CaioCCosta/indutor-dynavap/caixa-3d/decals/src/tribal_1.jpg

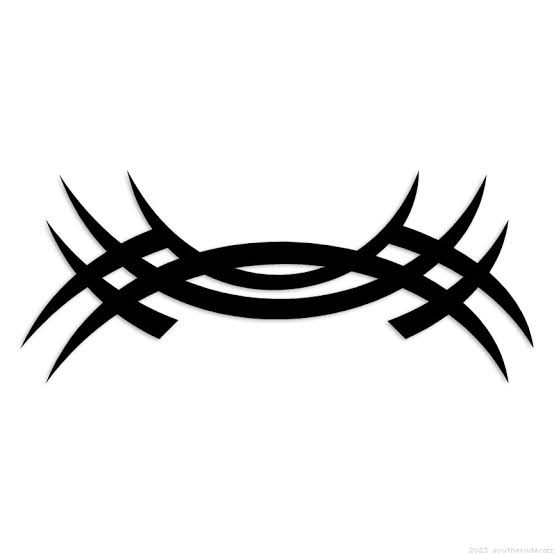
caixa-3d/decals/src/tribal_1.jpg
