CaioCCosta/indutor-dynavap/caixa-3d/decals/src/tribal_2.jpg

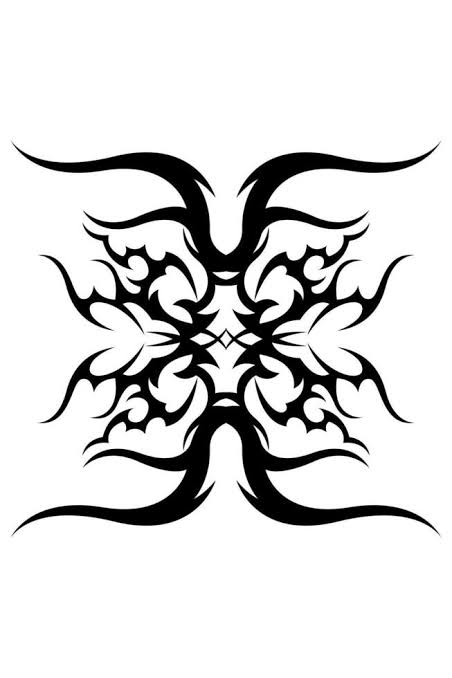
caixa-3d/decals/src/tribal_2.jpg
