CaioCCosta/indutor-dynavap/caixa-3d/stl/previews/body_bottom.png

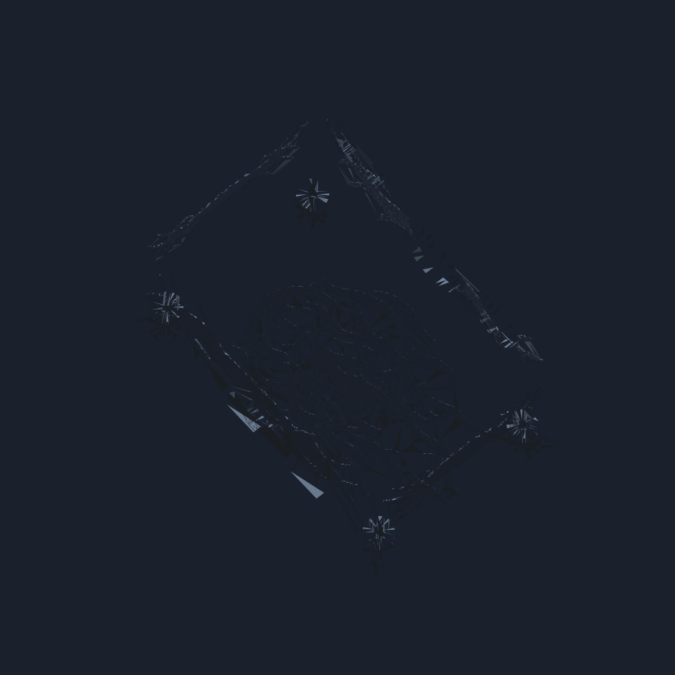
caixa-3d/stl/previews/body_bottom.png
