CaioCCosta/indutor-dynavap/caixa-3d/stl/previews/body_front.png

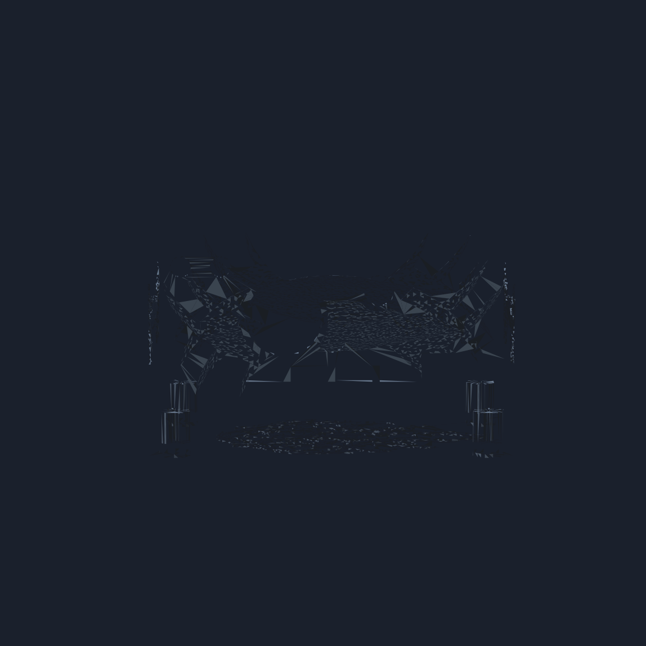
caixa-3d/stl/previews/body_front.png
