CaioCCosta/indutor-dynavap/caixa-3d/stl/previews/body_side.png

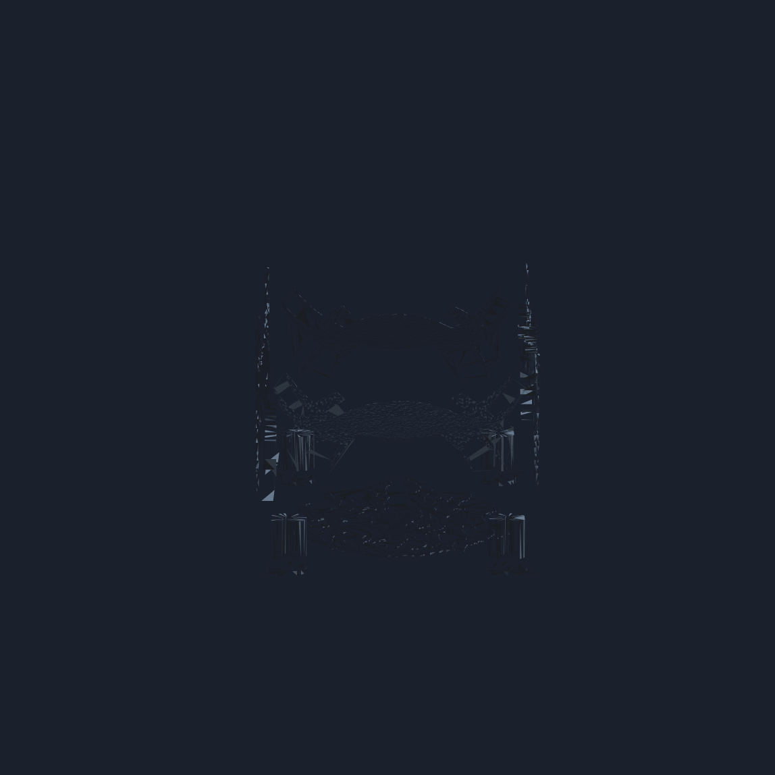
caixa-3d/stl/previews/body_side.png
