CaioCCosta/indutor-dynavap/caixa-3d/stl/previews/diag_front_xz.png

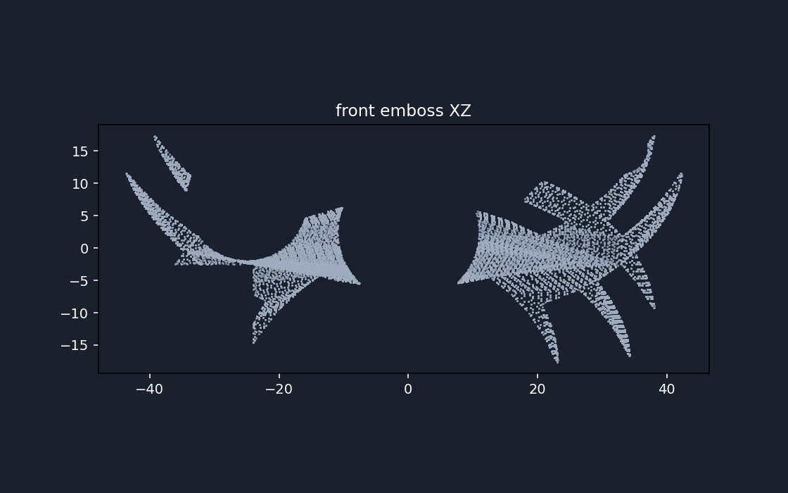
caixa-3d/stl/previews/diag_front_xz.png
