CaioCCosta/indutor-dynavap/caixa-3d/stl/previews/diag_left_yz.png

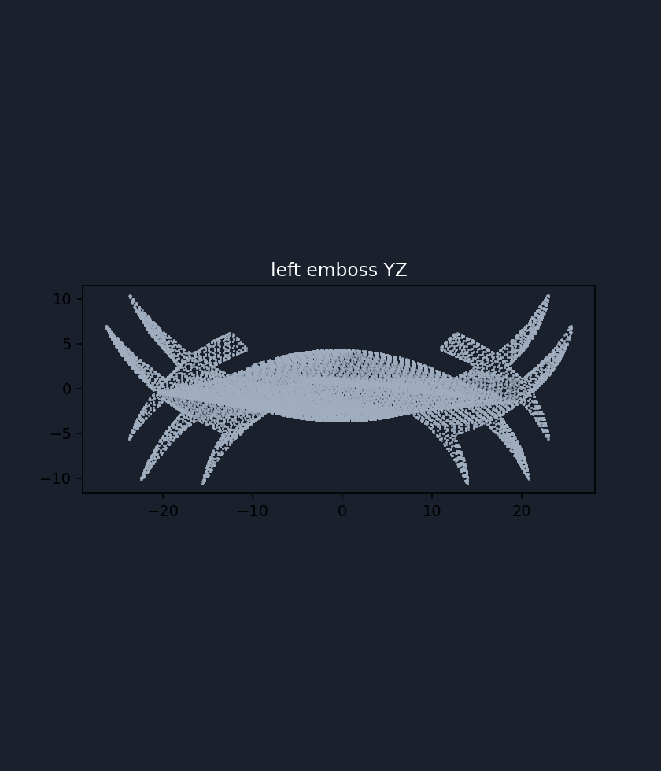
caixa-3d/stl/previews/diag_left_yz.png
