CaioCCosta/indutor-dynavap/caixa-3d/stl/previews/lid_fill_contrast.png

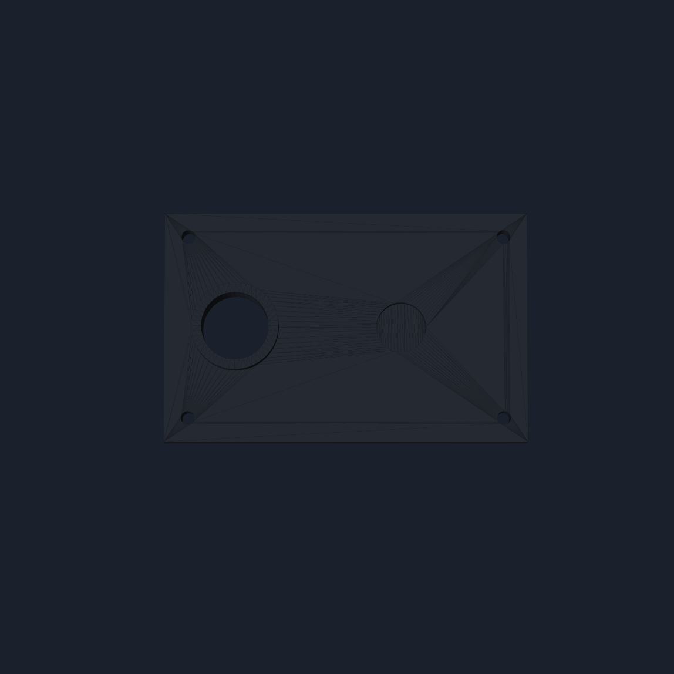
caixa-3d/stl/previews/lid_fill_contrast.png
