CaioCCosta/indutor-dynavap/caixa-3d/stl/previews/lid_full_iso.png

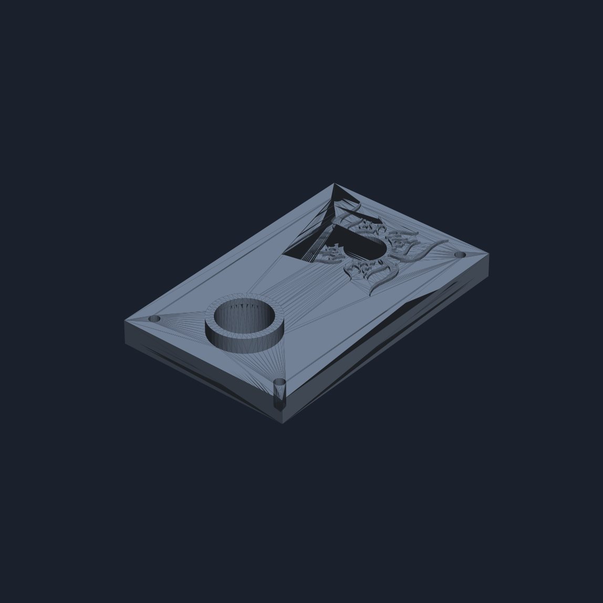
caixa-3d/stl/previews/lid_full_iso.png
