CaioCCosta/indutor-dynavap/caixa-3d/stl/previews/lid_full_top.png

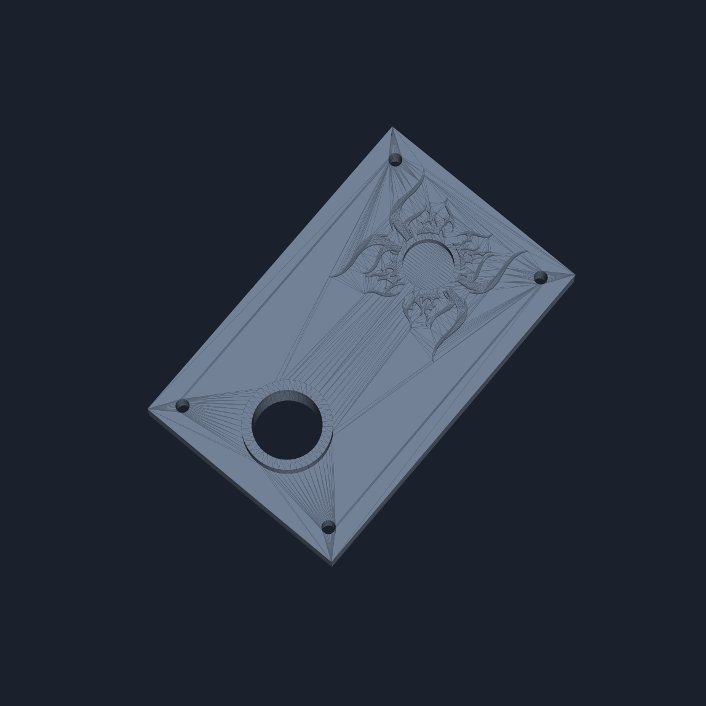
caixa-3d/stl/previews/lid_full_top.png
