CaioCCosta/indutor-dynavap/caixa-3d/stl/previews/lid_top.png

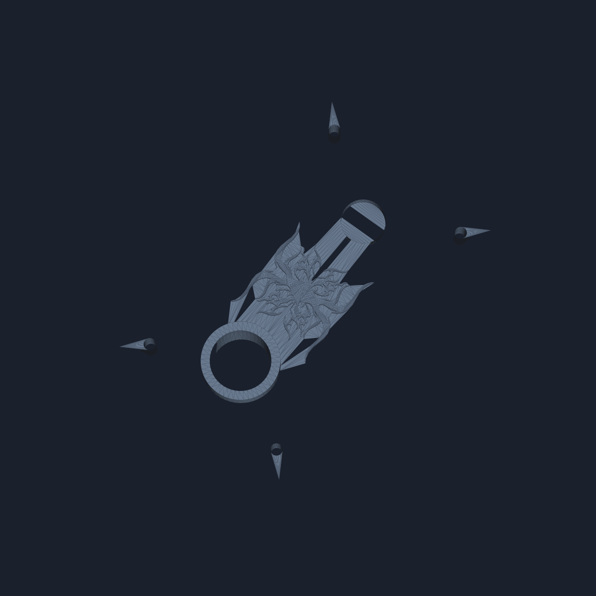
caixa-3d/stl/previews/lid_top.png
