CaioCCosta/indutor-dynavap/caixa-3d/stl/previews/ortho_bottom.png

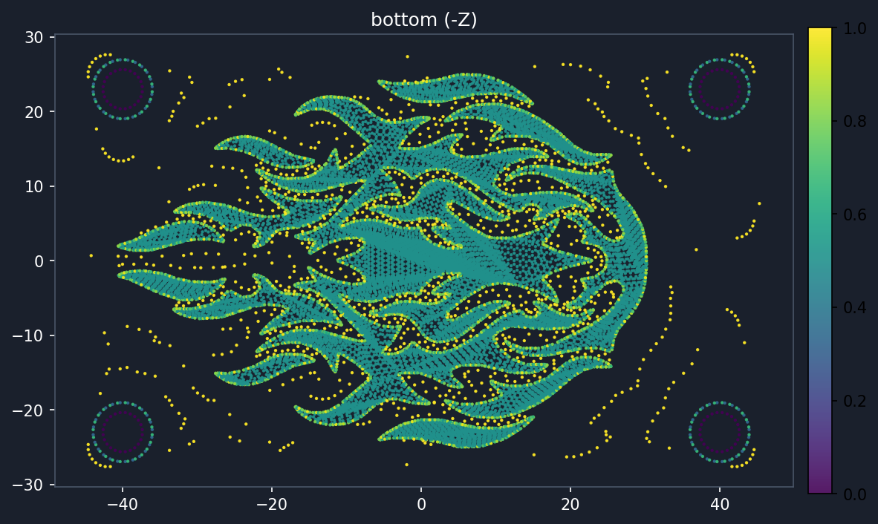
caixa-3d/stl/previews/ortho_bottom.png
