CaioCCosta/indutor-dynavap/caixa-3d/stl/previews/ortho_front.png

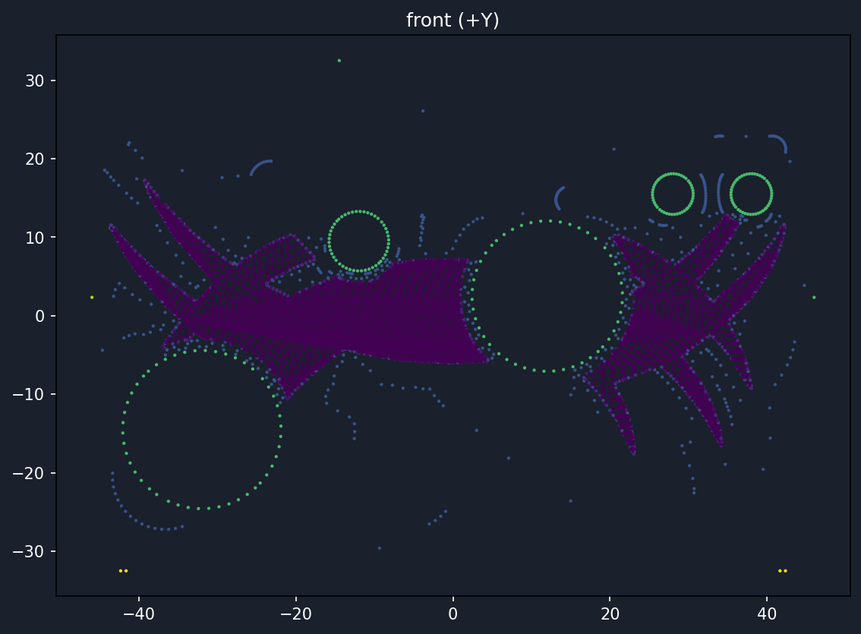
caixa-3d/stl/previews/ortho_front.png
