CaioCCosta/indutor-dynavap/caixa-3d/stl/previews/ortho_front_holes.png

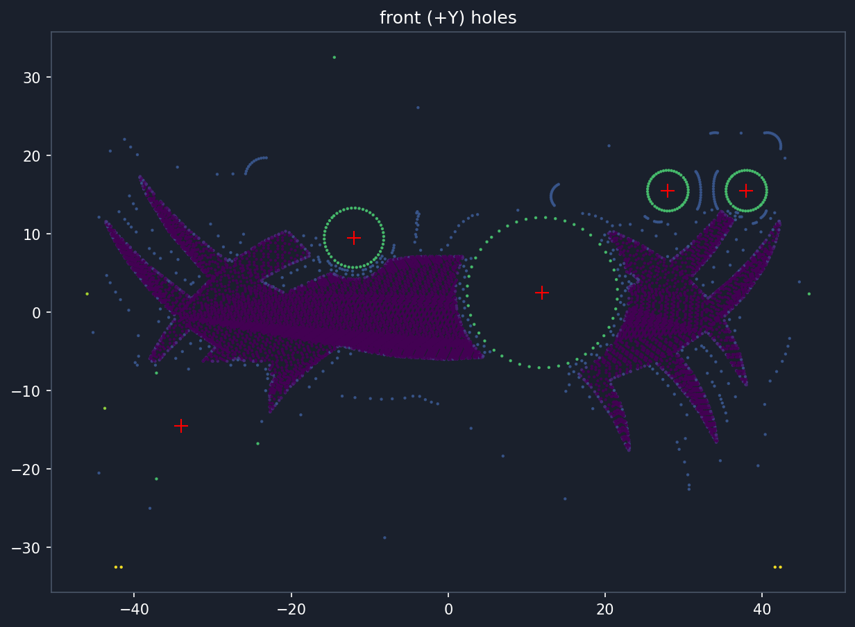
caixa-3d/stl/previews/ortho_front_holes.png
