CaioCCosta/indutor-dynavap/caixa-3d/stl/previews/ortho_lid.png

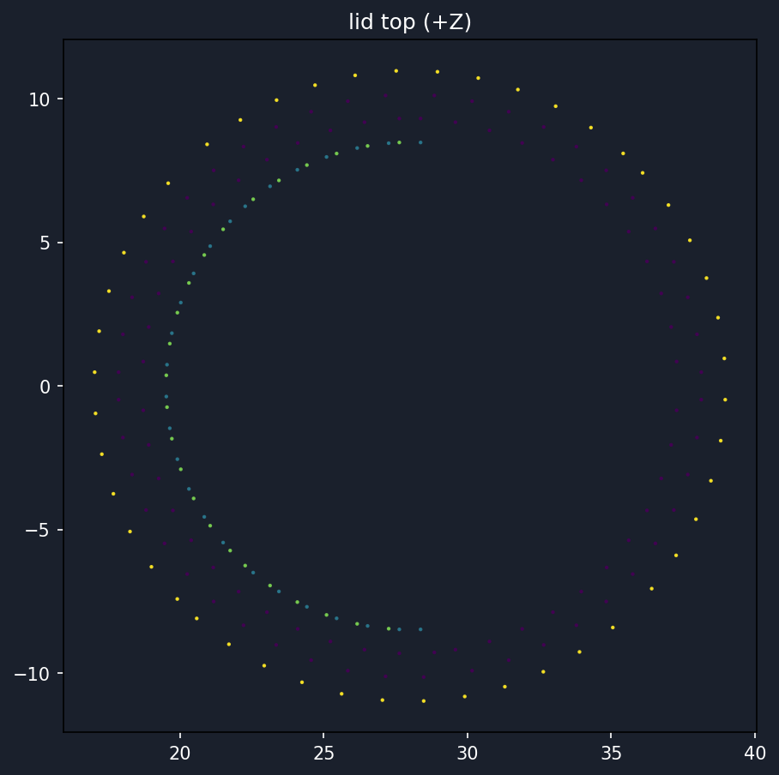
caixa-3d/stl/previews/ortho_lid.png
