CaioCCosta/indutor-dynavap/caixa-3d/stl/previews/ortho_right.png

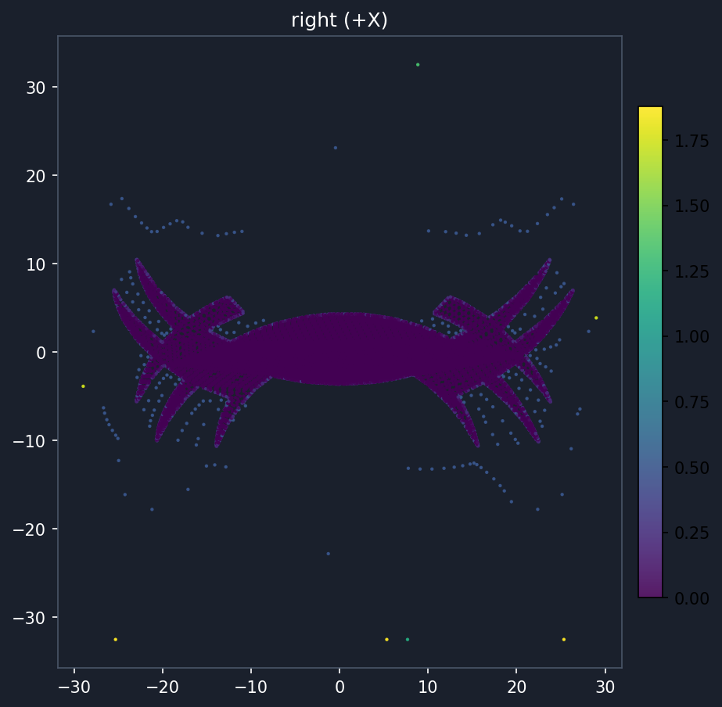
caixa-3d/stl/previews/ortho_right.png
