CaioCCosta/indutor-dynavap/caixa-3d/print/v1-cavas/decais.stl

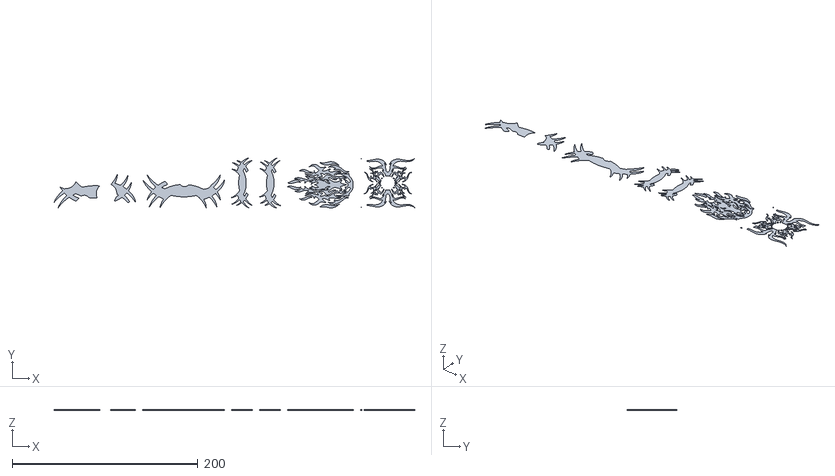
[picture p37: CAD file, 2026-09-03]
caixa-3d/print/v1-cavas/decais.stl
388.5 x 53.7 x 0.5
