CaioCCosta/indutor-dynavap/caixa-3d/print/v1-cavas/decal_tampa.stl

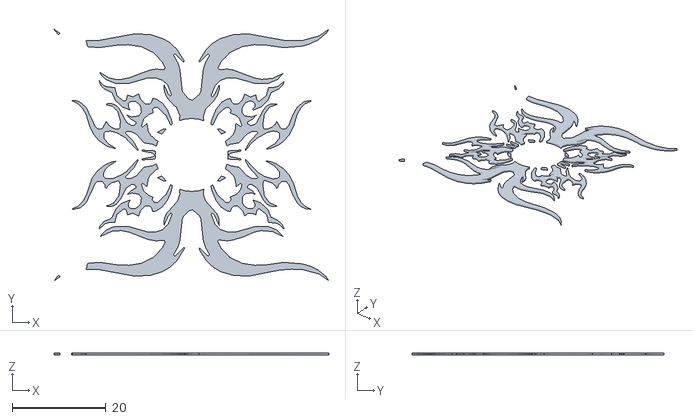
[picture p38: CAD file, 2026-09-03]
caixa-3d/print/v1-cavas/decal_tampa.stl
58.5 x 53.6 x 0.5
