CaioCCosta/indutor-dynavap/caixa-3d/stl/box_body.stl

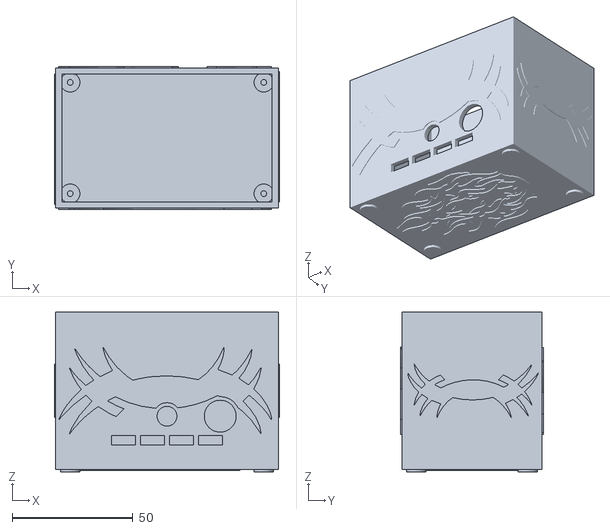
[picture p39: CAD file, 2026-09-03]
caixa-3d/stl/box_body.stl
93.0 x 59.0 x 66.0
