CaioCCosta/indutor-dynavap/caixa-3d/stl/previews/part_front.stl

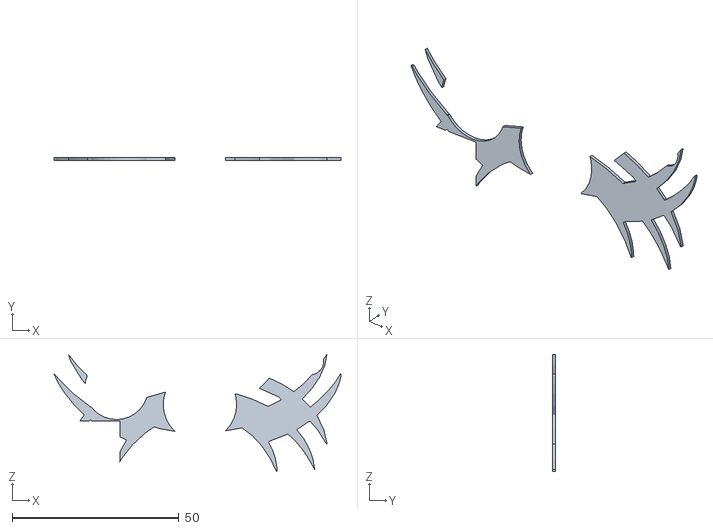
[picture p40: CAD file, 2026-09-03]
caixa-3d/stl/previews/part_front.stl
86.0 x 0.8 x 35.2
