CaioCCosta/indutor-dynavap/caixa-3d/print/v1-cavas/corpo_cava.stl

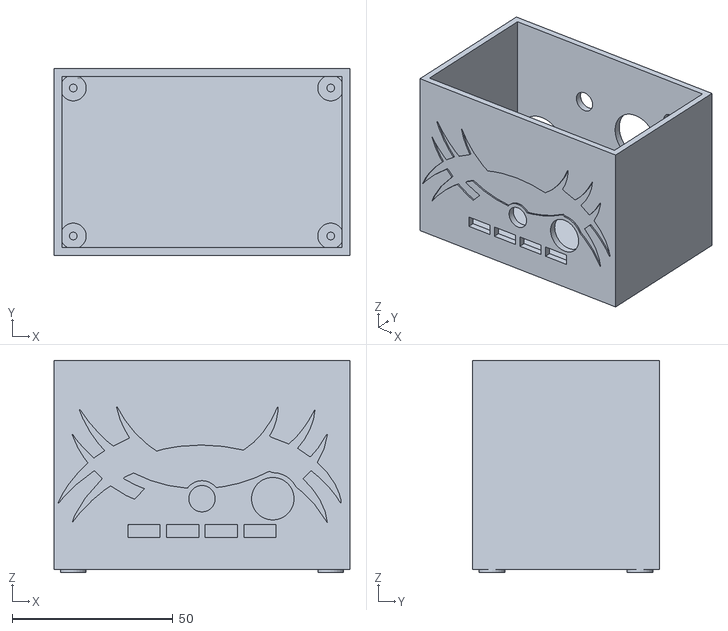
[picture p41: CAD file, 2026-09-03]
caixa-3d/print/v1-cavas/corpo_cava.stl
92.0 x 58.0 x 66.0
