CaioCCosta/indutor-dynavap/caixa-3d/stl/previews/part_rear.stl

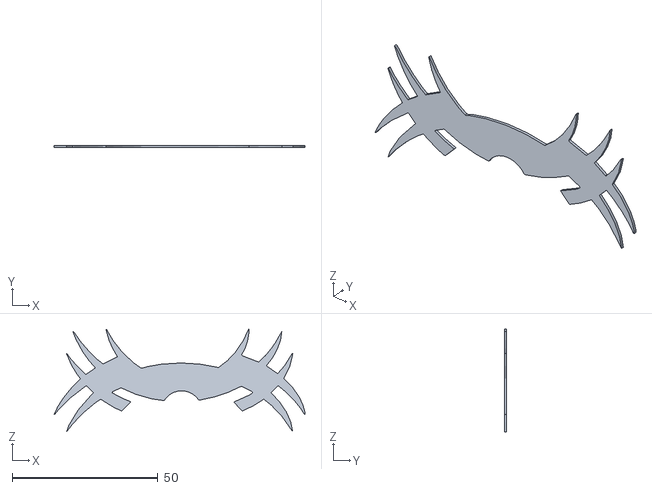
[picture p42: CAD file, 2026-09-03]
caixa-3d/stl/previews/part_rear.stl
86.0 x 0.8 x 35.2
