CaioCCosta/indutor-dynavap/caixa-3d/stl/box_body_base.stl

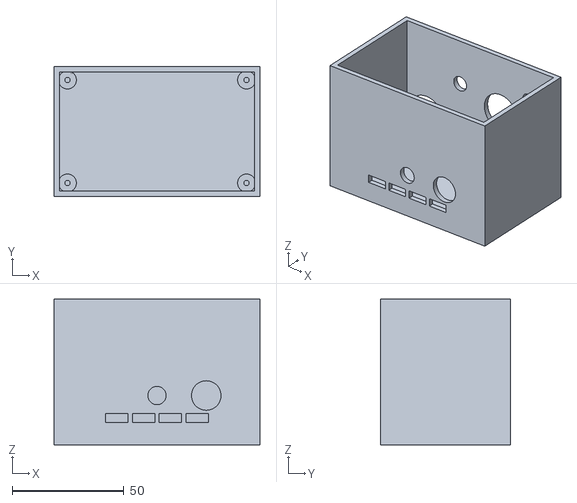
[picture p43: CAD file, 2026-09-03]
caixa-3d/stl/box_body_base.stl
92.0 x 58.0 x 65.0
