CaioCCosta/indutor-dynavap/caixa-3d/print/v1-cavas/decal_dir.stl

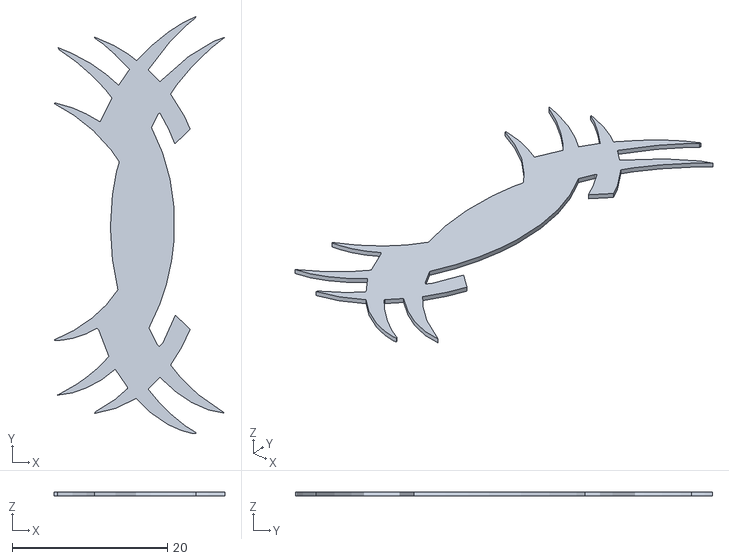
[picture p44: CAD file, 2026-09-03]
caixa-3d/print/v1-cavas/decal_dir.stl
22.0 x 53.7 x 0.5
