CaioCCosta/indutor-dynavap/caixa-3d/stl/previews/part_bottom.stl

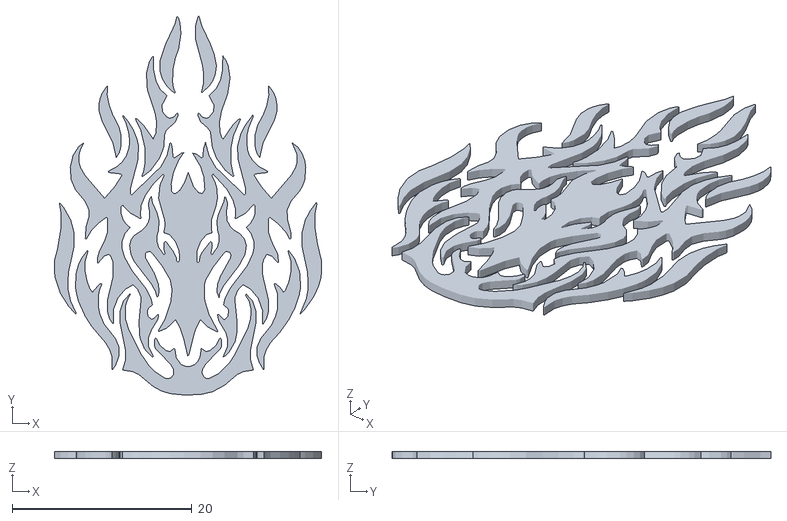
[picture p45: CAD file, 2026-09-03]
caixa-3d/stl/previews/part_bottom.stl
29.8 x 42.2 x 0.8
