CaioCCosta/indutor-dynavap/caixa-3d/stl/previews/assembly_front.png

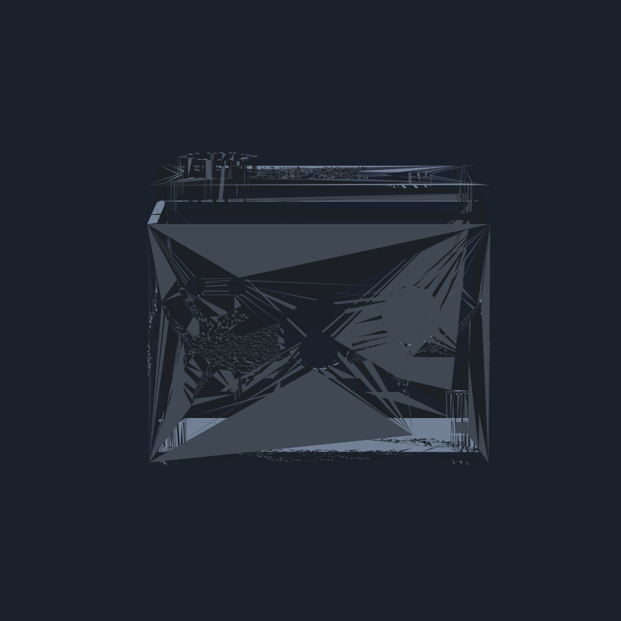
caixa-3d/stl/previews/assembly_front.png
