CaioCCosta/indutor-dynavap/caixa-3d/stl/previews/assembly_iso.png

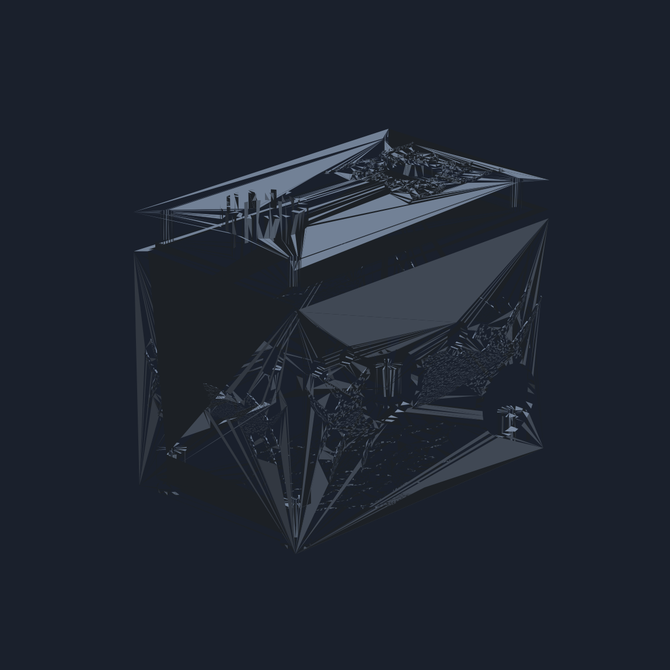
caixa-3d/stl/previews/assembly_iso.png
